ri-buni/Wild-clock-with-Emnny/Firmware/bitmaps.h

// ============================================================================
// bitmaps.h — 27x27 monochrome bunny frames
// format: 4 bytes per row (27 px rounded up to 32), 27 rows = 108 bytes/frame
// MSB-first, u8g2-compatible (use drawXBM or drawBitmap with rotation=0)
// ============================================================================
//
// PLACEHOLDER ART BELOW. when you send me the 4 PNGs I'll replace these arrays
// with the real pixel data. for now you'll see crude bunny shapes so you can
// verify the display works.
// ============================================================================
#pragma once
#include <Arduino.h>

#define BUNNY_W 27
#define BUNNY_H 27

// each row is 4 bytes (32 bits, last 5 unused), MSB-first
// bit = 1 -> pixel ON (lit on OLED)

// -------- NEUTRAL FRAME A (eyes open) ---------------------------------------
const uint8_t BUNNY_NEUTRAL_A[] PROGMEM = {
  0x18,0x18,0x00,0x00,  //    ##   ##
  0x3C,0x3C,0x00,0x00,  //   ####  ####
  0x3C,0x3C,0x00,0x00,  //   ####  ####
  0x3C,0x3C,0x00,0x00,  //   ####  ####
  0x3E,0x7C,0x00,0x00,  //   ##### #####
  0x1F,0xF8,0x00,0x00,  //    ##########
  0x0F,0xF0,0x00,0x00,  //     ########
  0x1F,0xF8,0x00,0x00,  //    ##########
  0x3F,0xFC,0x00,0x00,  //   ############
  0x7F,0xFE,0x00,0x00,  //  ##############
  0x7C,0xFE,0x00,0x00,  //  ##### ########
  0x70,0x0E,0x00,0x00,  //  ###       ###     (eyes!)
  0x7C,0xFE,0x00,0x00,  //  ##### ########
  0x7F,0xFE,0x00,0x00,  //  ##############
  0x7F,0xFE,0x00,0x00,  //  ##############
  0x7F,0x9E,0x00,0x00,  //  ######## ####
  0x7F,0xFE,0x00,0x00,  //  ##############     (nose ~here)
  0x3F,0xFC,0x00,0x00,  //   ############
  0x3F,0xFC,0x00,0x00,  //   ############
  0x1F,0xF8,0x00,0x00,  //    ##########
  0x0F,0xF0,0x00,0x00,  //     ########
  0x07,0xE0,0x00,0x00,  //      ######
  0x03,0xC0,0x00,0x00,  //       ####
  0x01,0x80,0x00,0x00,  //        ##
  0x00,0x00,0x00,0x00,
  0x00,0x00,0x00,0x00,
  0x00,0x00,0x00,0x00,
};

// -------- NEUTRAL FRAME B (eyes blinking — eyes are closed/squinted) -------
const uint8_t BUNNY_NEUTRAL_B[] PROGMEM = {
  0x18,0x18,0x00,0x00,
  0x3C,0x3C,0x00,0x00,
  0x3C,0x3C,0x00,0x00,
  0x3C,0x3C,0x00,0x00,
  0x3E,0x7C,0x00,0x00,
  0x1F,0xF8,0x00,0x00,
  0x0F,0xF0,0x00,0x00,
  0x1F,0xF8,0x00,0x00,
  0x3F,0xFC,0x00,0x00,
  0x7F,0xFE,0x00,0x00,
  0x7F,0xFE,0x00,0x00,
  0x7F,0xFE,0x00,0x00,  // eyes closed: solid line
  0x7C,0xFE,0x00,0x00,
  0x7F,0xFE,0x00,0x00,
  0x7F,0xFE,0x00,0x00,
  0x7F,0x9E,0x00,0x00,
  0x7F,0xFE,0x00,0x00,
  0x3F,0xFC,0x00,0x00,
  0x3F,0xFC,0x00,0x00,
  0x1F,0xF8,0x00,0x00,
  0x0F,0xF0,0x00,0x00,
  0x07,0xE0,0x00,0x00,
  0x03,0xC0,0x00,0x00,
  0x01,0x80,0x00,0x00,
  0x00,0x00,0x00,0x00,
  0x00,0x00,0x00,0x00,
  0x00,0x00,0x00,0x00,
};

// -------- SLEEPING FRAME A (curled, breathing in) ---------------------------
const uint8_t BUNNY_SLEEP_A[] PROGMEM = {
  0x00,0x00,0x00,0x00,
  0x00,0x00,0x00,0x00,
  0x00,0x00,0x00,0x00,
  0x00,0x18,0x00,0x00,  //          ##     (ear flopped)
  0x00,0x3C,0x00,0x00,
  0x00,0x7E,0x00,0x00,
  0x03,0xFF,0x00,0x00,  //       ##########
  0x07,0xFF,0x80,0x00,  //      ############
  0x0F,0xFF,0xC0,0x00,
  0x1F,0xFF,0xE0,0x00,
  0x3F,0xFF,0xE0,0x00,
  0x3F,0xCF,0xE0,0x00,  // closed eye line
  0x7F,0xFF,0xF0,0x00,
  0x7F,0xFF,0xF0,0x00,
  0x7F,0xFF,0xF0,0x00,
  0x3F,0xFF,0xE0,0x00,
  0x3F,0xFF,0xE0,0x00,
  0x1F,0xFF,0xC0,0x00,
  0x0F,0xFF,0x80,0x00,
  0x07,0xFF,0x00,0x00,
  0x03,0xFE,0x00,0x00,
  0x01,0xFC,0x00,0x00,
  0x00,0xF8,0x00,0x00,
  0x00,0x00,0x00,0x00,
  0x00,0x00,0x00,0x00,
  0x00,0x00,0x00,0x00,
  0x00,0x00,0x00,0x00,
};

// -------- SLEEPING FRAME B (curled, breathing out — slightly smaller) ------
const uint8_t BUNNY_SLEEP_B[] PROGMEM = {
  0x00,0x00,0x00,0x00,
  0x00,0x00,0x00,0x00,
  0x00,0x00,0x00,0x00,
  0x00,0x00,0x00,0x00,
  0x00,0x18,0x00,0x00,
  0x00,0x3C,0x00,0x00,
  0x01,0xFE,0x00,0x00,
  0x03,0xFF,0x00,0x00,
  0x07,0xFF,0x80,0x00,
  0x0F,0xFF,0xC0,0x00,
  0x1F,0xFF,0xE0,0x00,
  0x1F,0xCF,0xE0,0x00,
  0x3F,0xFF,0xF0,0x00,
  0x3F,0xFF,0xF0,0x00,
  0x3F,0xFF,0xF0,0x00,
  0x1F,0xFF,0xE0,0x00,
  0x1F,0xFF,0xE0,0x00,
  0x0F,0xFF,0xC0,0x00,
  0x07,0xFF,0x80,0x00,
  0x03,0xFF,0x00,0x00,
  0x01,0xFE,0x00,0x00,
  0x00,0xFC,0x00,0x00,
  0x00,0x00,0x00,0x00,
  0x00,0x00,0x00,0x00,
  0x00,0x00,0x00,0x00,
  0x00,0x00,0x00,0x00,
  0x00,0x00,0x00,0x00,
};
